TaISLab/pHRI-Hand-4F-Compliant/Pictures/IMG_0030.JPEG

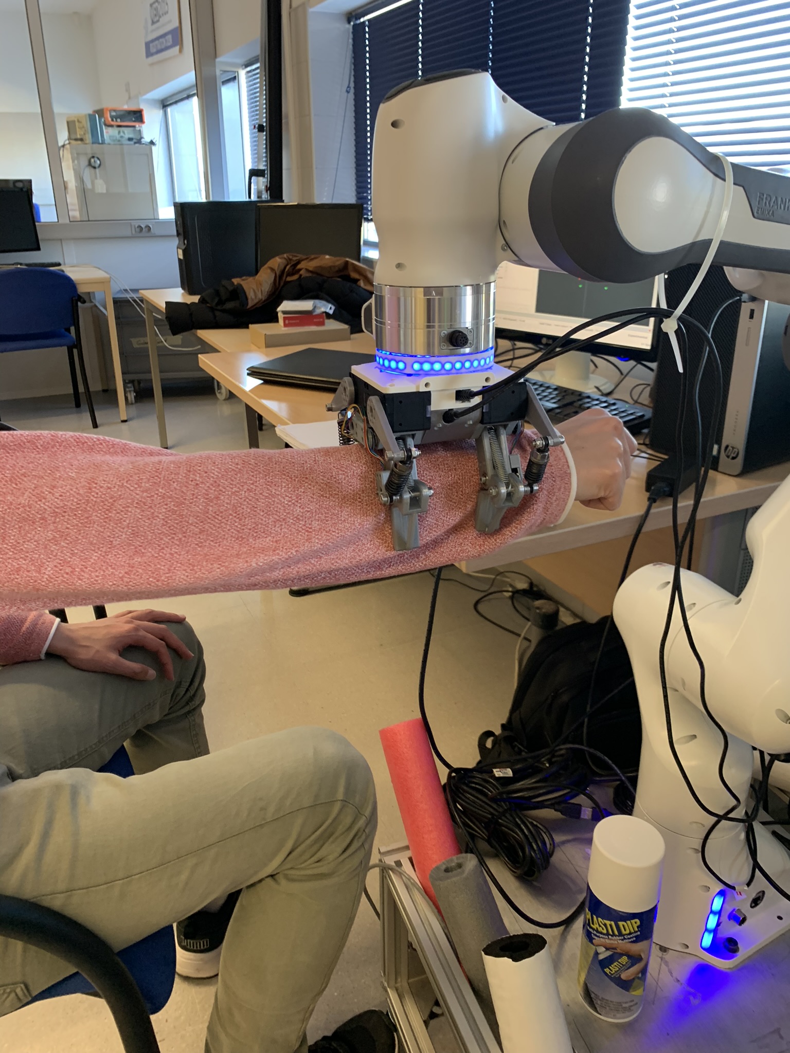
Pictures/IMG_0030.JPEG
