TaISLab/pHRI-Hand-4F-Compliant/CAD/base-servos.SLDPRT

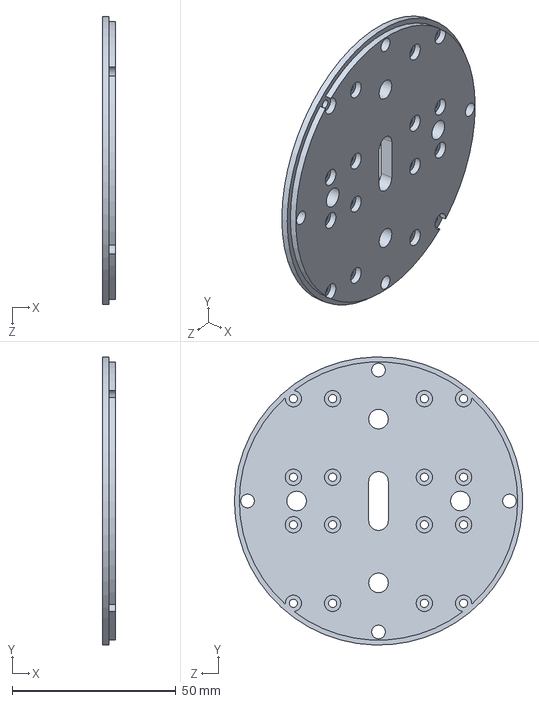
[picture p20: CAD file, 2024-05-29]
CAD/base-servos.SLDPRT
4.00 x 88.0 x 88.0 mm
