TaISLab/pHRI-Hand-4F-Compliant/CAD/potentiometers/potaxis.SLDPRT

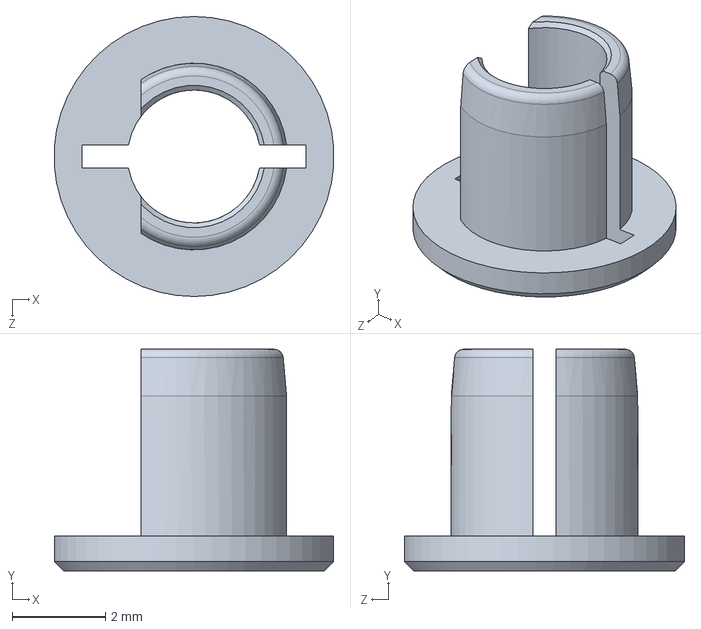
[picture p21: CAD file, 2024-05-29]
CAD/potentiometers/potaxis.SLDPRT
5.99 x 4.75 x 6.00 mm
