TaISLab/pHRI-Hand-4F-Compliant/CAD/Palo1.SLDPRT

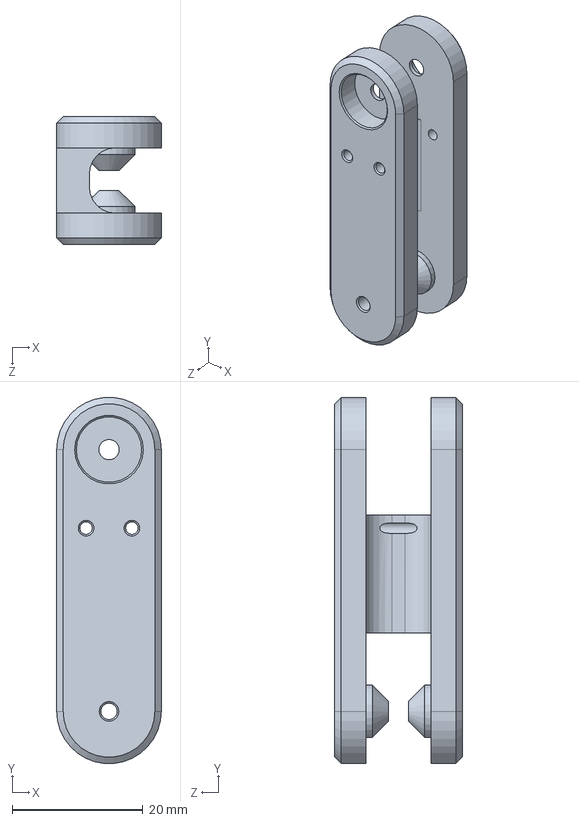
[picture p22: CAD file, 2024-05-29]
CAD/Palo1.SLDPRT
16.0 x 55.9 x 19.5 mm
