TaISLab/pHRI-Hand-4F-Compliant/CAD/biela servo.SLDPRT

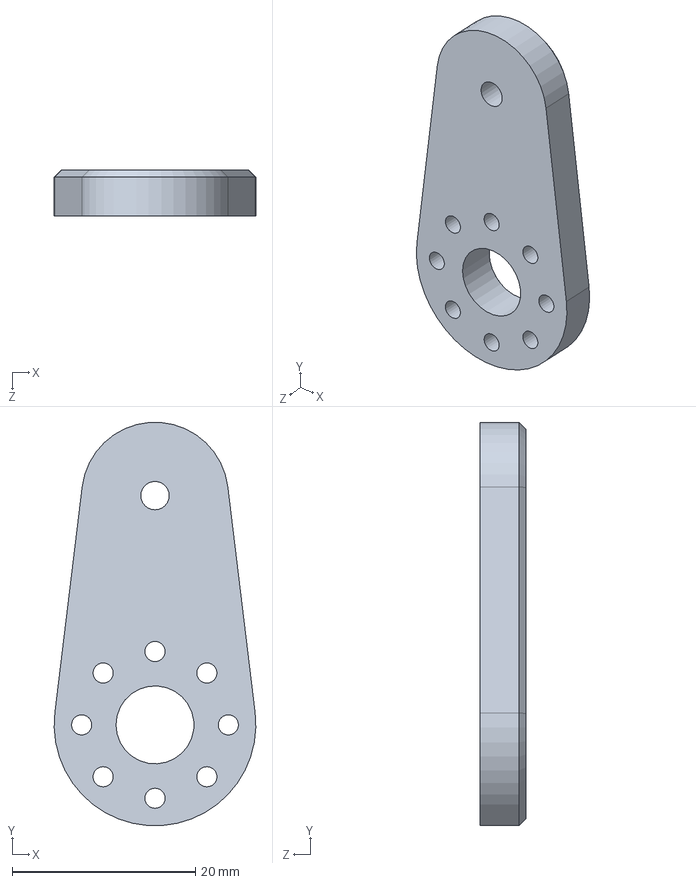
[picture p23: CAD file, 2024-05-29]
CAD/biela servo.SLDPRT
22.0 x 43.9 x 5.00 mm
