TaISLab/pHRI-Hand-4F-Compliant/CAD/Amortecedor (PRONTO).SLDPRT

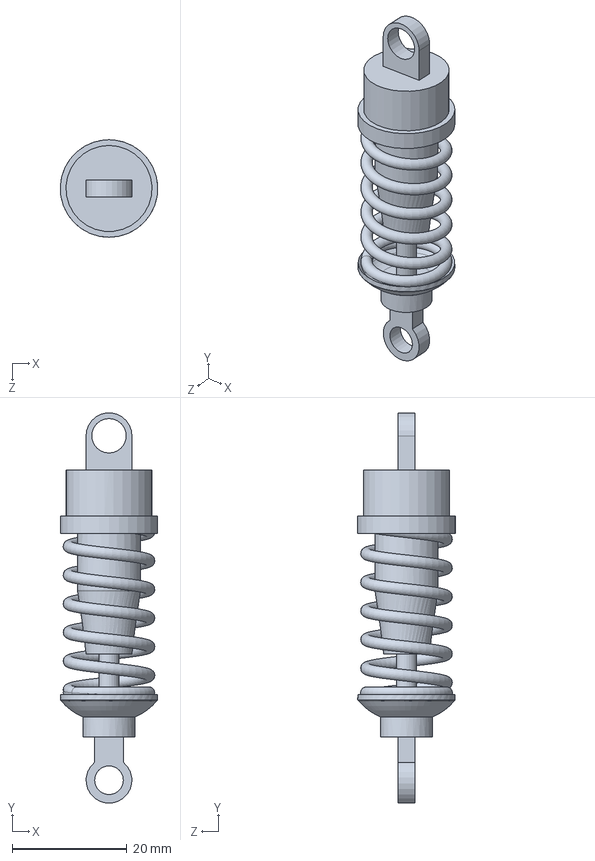
[picture p24: CAD file, 2024-05-29]
CAD/Amortecedor (PRONTO).SLDPRT
17.0 x 67.9 x 17.0 mm
