TaISLab/pHRI-Hand-4F-Compliant/CAD/biela servo 2-50.SLDPRT

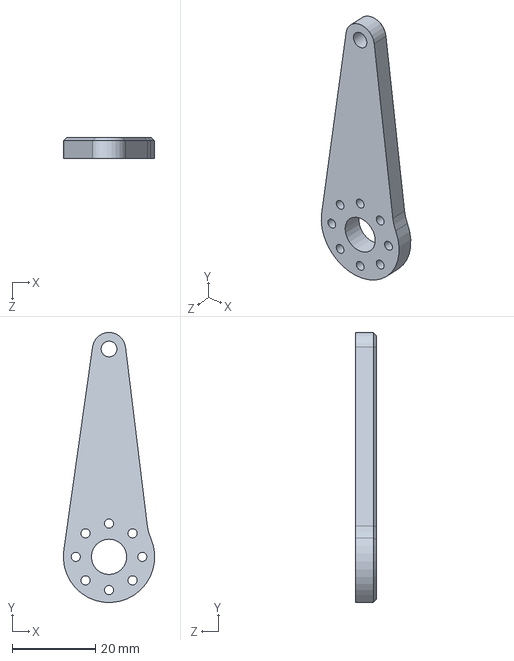
[picture p25: CAD file, 2024-05-29]
CAD/biela servo 2-50.SLDPRT
22.0 x 65.0 x 5.00 mm
