TaISLab/pHRI-Hand-4F-Compliant/CAD/base-robot-4.SLDPRT

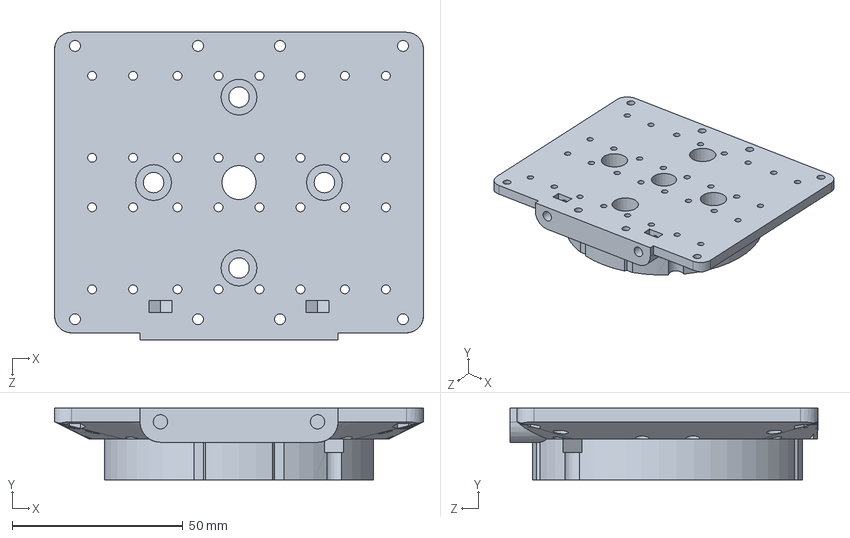
[picture p26: CAD file, 2024-05-29]
CAD/base-robot-4.SLDPRT
108.0 x 21.0 x 90.0 mm
