TaISLab/pHRI-Hand-4F-Compliant/CAD/biela servo 2-45.SLDPRT

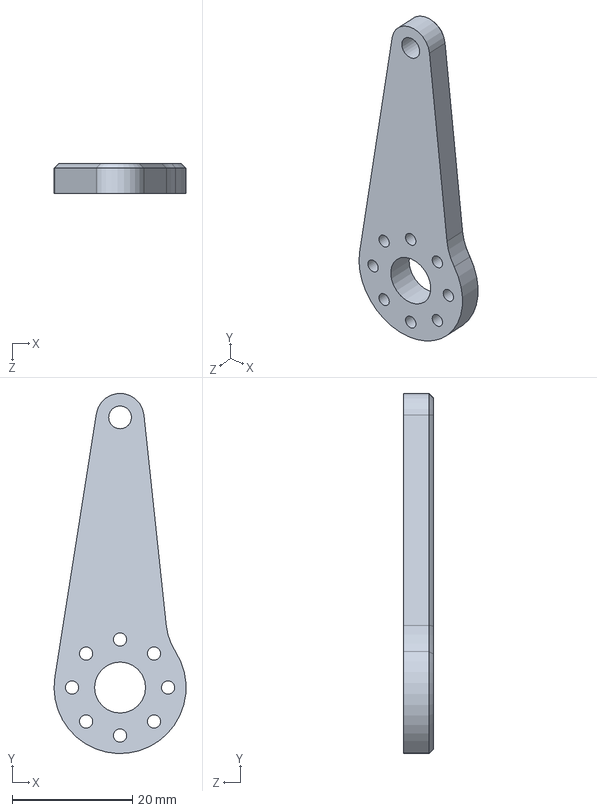
[picture p27: CAD file, 2024-05-29]
CAD/biela servo 2-45.SLDPRT
22.0 x 60.0 x 5.00 mm
