TaISLab/pHRI-Hand-4F-Compliant/CAD/Palo2.SLDPRT

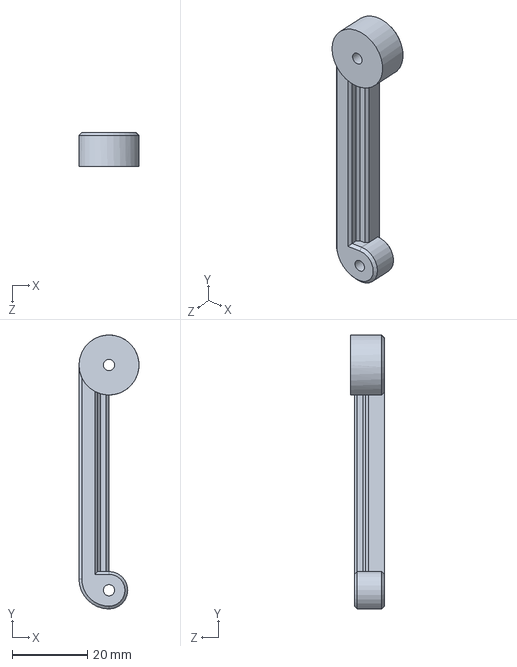
[picture p28: CAD file, 2024-05-29]
CAD/Palo2.SLDPRT
16.0 x 73.0 x 9.00 mm
