TaISLab/pHRI-Hand-4F-Compliant/CAD/pico20-ligero.SLDPRT

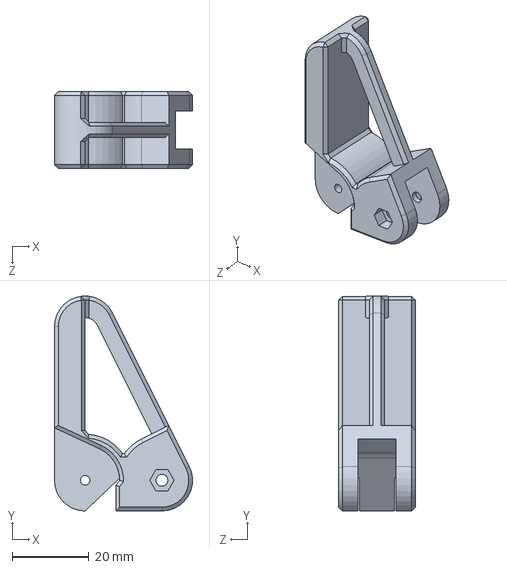
[picture p29: CAD file, 2024-05-29]
CAD/pico20-ligero.SLDPRT
36.0 x 56.0 x 20.0 mm
