TaISLab/pHRI-Hand-4F-Compliant/CAD/module.SLDPRT

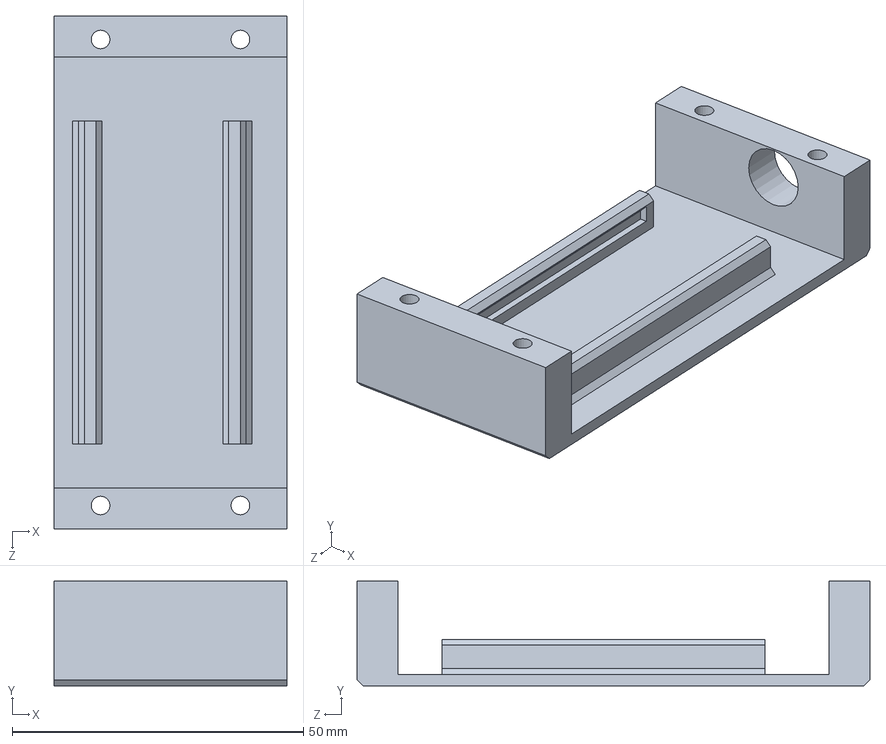
[picture p30: CAD file, 2024-05-29]
CAD/module.SLDPRT
40.0 x 18.0 x 88.0 mm
