TaISLab/pHRI-Hand-4F-Compliant/CAD/base-robot2.SLDPRT

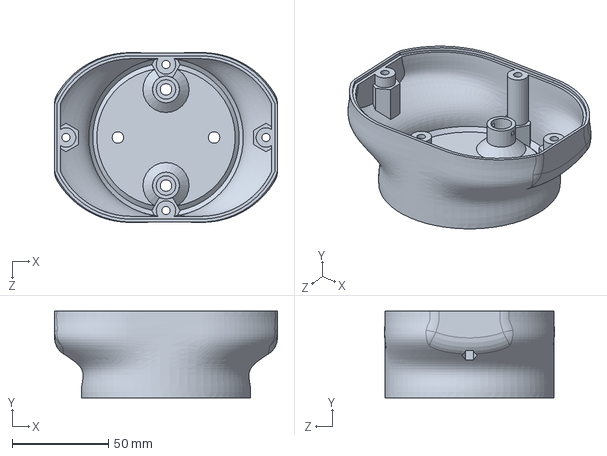
[picture p31: CAD file, 2024-05-29]
CAD/base-robot2.SLDPRT
116.0 x 45.0 x 88.3 mm
