TaISLab/pHRI-Hand-4F-Compliant/CAD/as5048a.SLDPRT

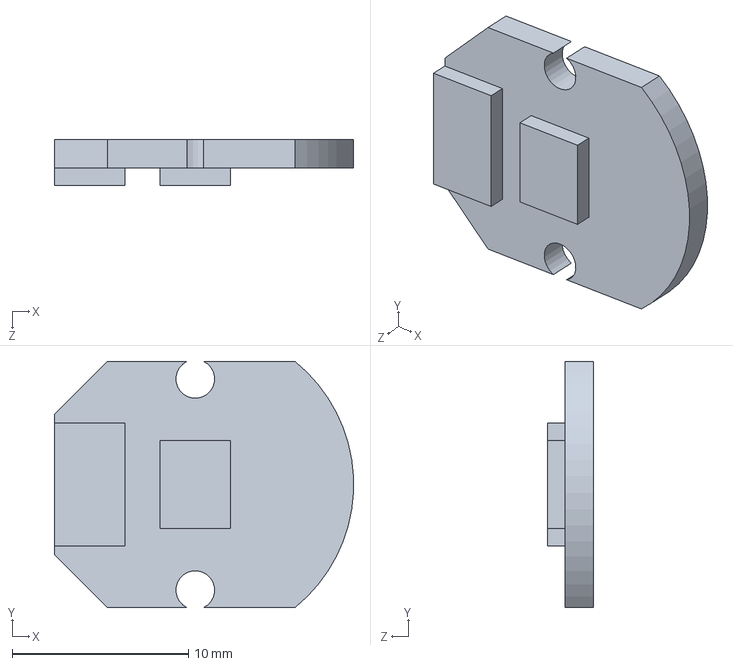
[picture p32: CAD file, 2024-05-29]
CAD/as5048a.SLDPRT
17.0 x 14.0 x 2.60 mm
