TaISLab/pHRI-Hand-4F-Compliant/CAD/biela servo 50.SLDPRT

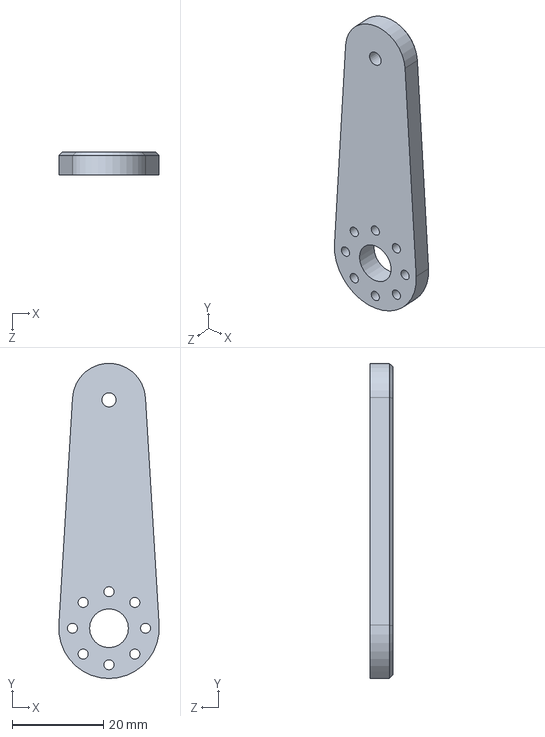
[picture p33: CAD file, 2024-05-29]
CAD/biela servo 50.SLDPRT
22.0 x 69.0 x 5.00 mm
