TaISLab/pHRI-Hand-4F-Compliant/CAD/baser-tobot-3.SLDPRT

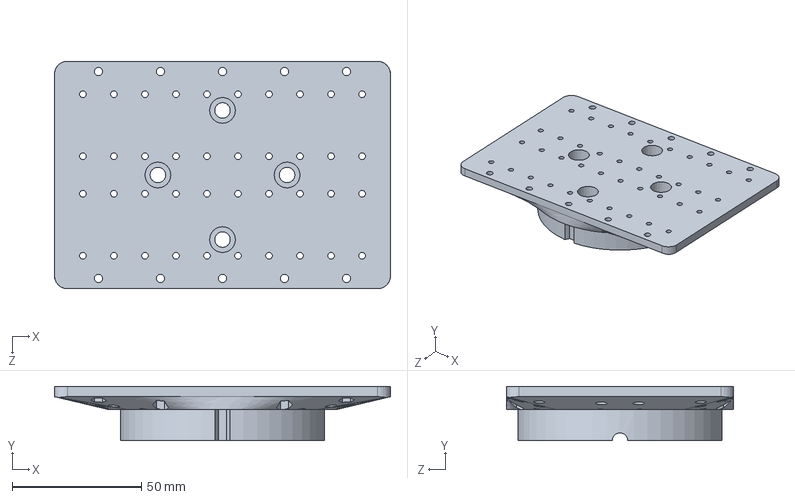
[picture p34: CAD file, 2024-05-29]
CAD/baser-tobot-3.SLDPRT
130.0 x 21.0 x 88.0 mm
