TaISLab/pHRI-Hand-4F-Compliant/CAD/biela servo 2.SLDPRT

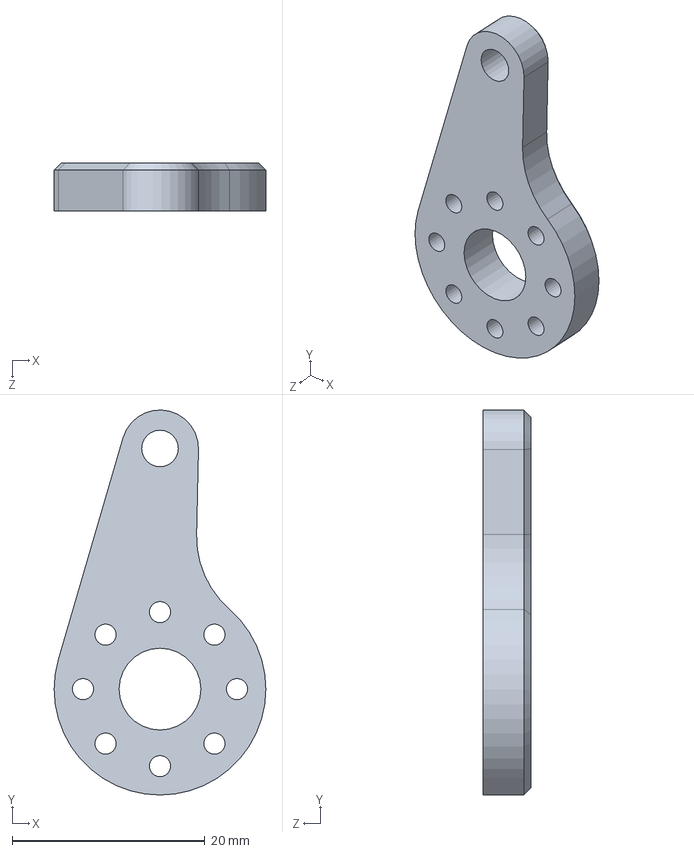
[picture p35: CAD file, 2024-05-29]
CAD/biela servo 2.SLDPRT
22.0 x 40.0 x 5.00 mm
