TaISLab/pHRI-Hand-4F-Compliant/CAD/biela servo 45.SLDPRT

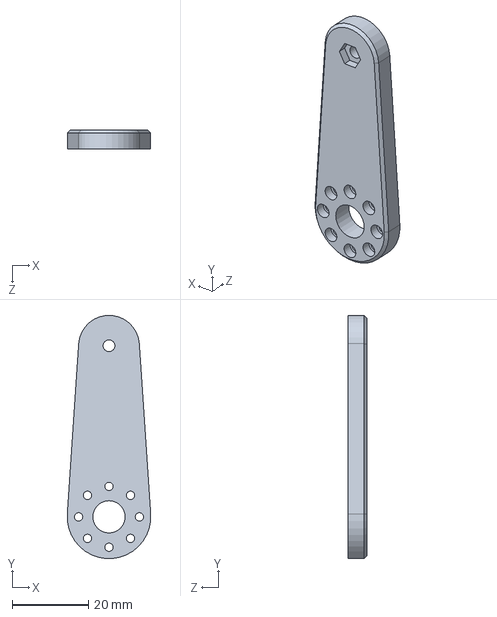
[picture p36: CAD file, 2024-05-29]
CAD/biela servo 45.SLDPRT
22.0 x 63.9 x 5.00 mm
