TaISLab/pHRI-Hand-4F-Compliant/CAD/forearm.SLDPRT

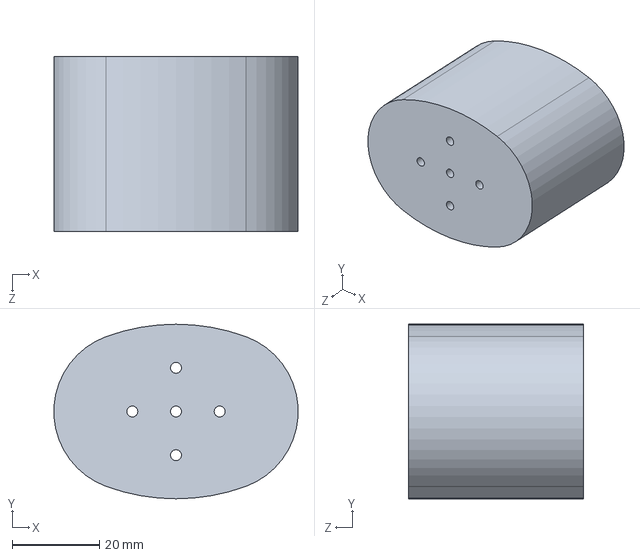
[picture p37: CAD file, 2024-05-29]
CAD/forearm.SLDPRT
55.9 x 40.0 x 40.0 mm
