TaISLab/pHRI-Hand-4F-Compliant/CAD/soporteencodersimple.SLDPRT

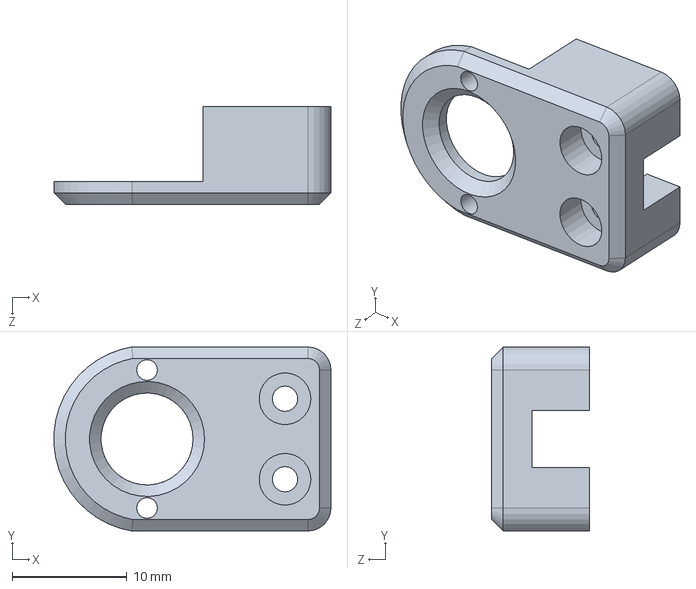
[picture p38: CAD file, 2024-05-29]
CAD/soporteencodersimple.SLDPRT
24.1 x 16.0 x 8.50 mm
