TaISLab/pHRI-Hand-4F-Compliant/CAD/soporteencoder.SLDPRT

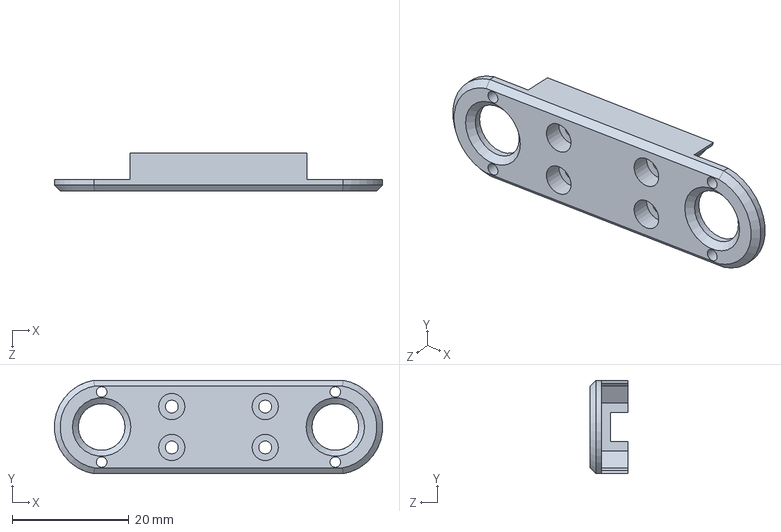
[picture p39: CAD file, 2024-05-29]
CAD/soporteencoder.SLDPRT
56.1 x 16.0 x 6.50 mm
