TaISLab/pHRI-Hand-4F-Compliant/CAD/module-chepa.SLDPRT

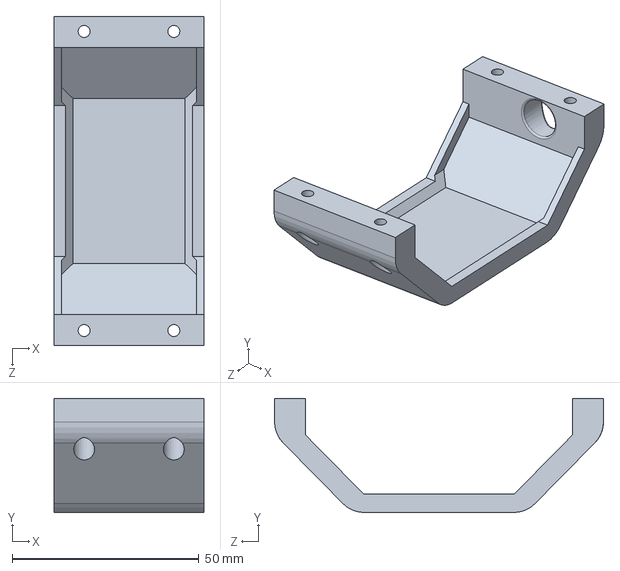
[picture p40: CAD file, 2024-05-29]
CAD/module-chepa.SLDPRT
40.0 x 30.5 x 88.0 mm
