TaISLab/pHRI-Hand-4F-Compliant/CAD/lgmount.SLDPRT

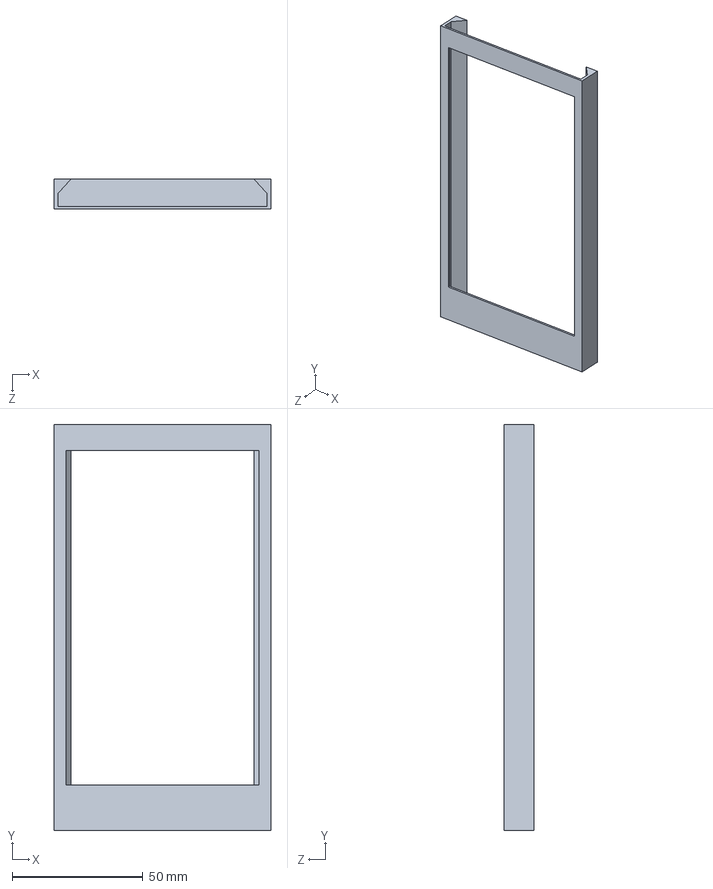
[picture p41: CAD file, 2024-05-29]
CAD/lgmount.SLDPRT
83.0 x 155.5 x 11.5 mm
