TaISLab/pHRI-Hand-4F-Compliant/CAD/base4.SLDPRT

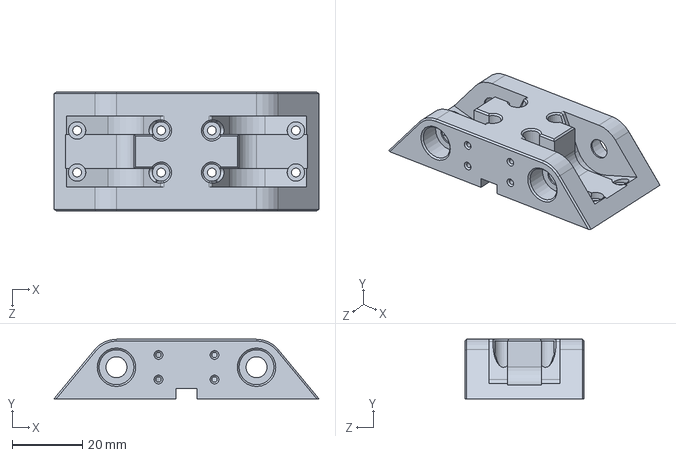
[picture p42: CAD file, 2024-05-29]
CAD/base4.SLDPRT
75.7 x 17.0 x 34.0 mm
