TaISLab/pHRI-Hand-4F-Compliant/CAD/biela servo 35.SLDPRT

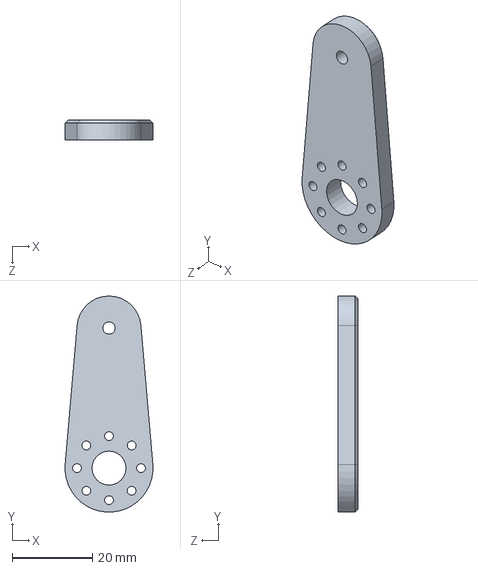
[picture p43: CAD file, 2024-05-29]
CAD/biela servo 35.SLDPRT
21.9 x 54.0 x 5.00 mm
