TaISLab/pHRI-Hand-4F-Compliant/CAD/pantalla led.SLDPRT

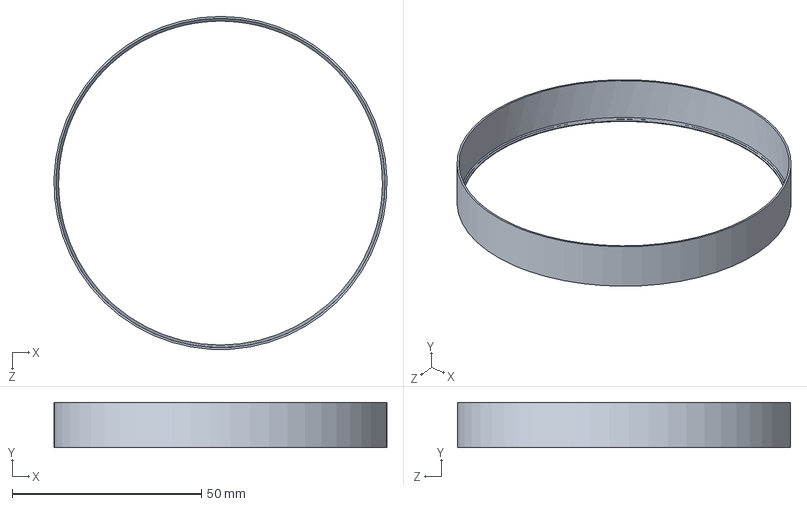
[picture p44: CAD file, 2024-05-29]
CAD/pantalla led.SLDPRT
88.0 x 12.0 x 88.0 mm
