TaISLab/pHRI-Hand-4F-Compliant/CAD/base-robot.SLDPRT

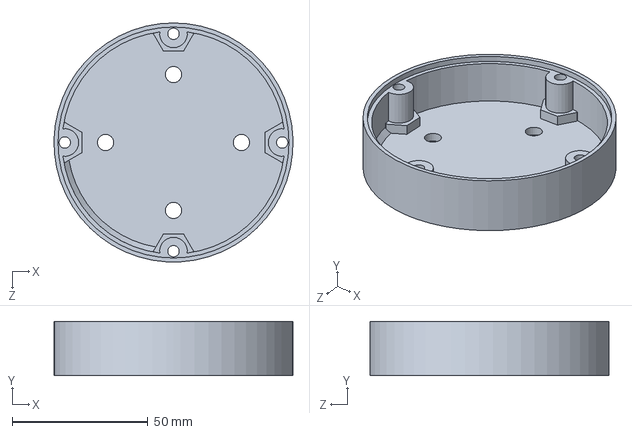
[picture p45: CAD file, 2024-05-29]
CAD/base-robot.SLDPRT
88.0 x 20.0 x 88.0 mm
