TaISLab/pHRI-Hand-4F-Compliant/CAD/acopla-top.SLDPRT

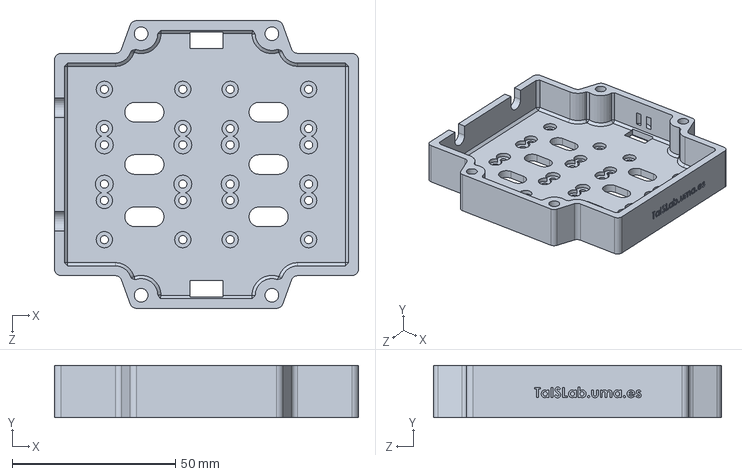
[picture p46: CAD file, 2024-05-29]
CAD/acopla-top.SLDPRT
93.0 x 16.0 x 88.0 mm
