TaISLab/pHRI-Hand-4F-Compliant/CAD/potBASE2.SLDPRT

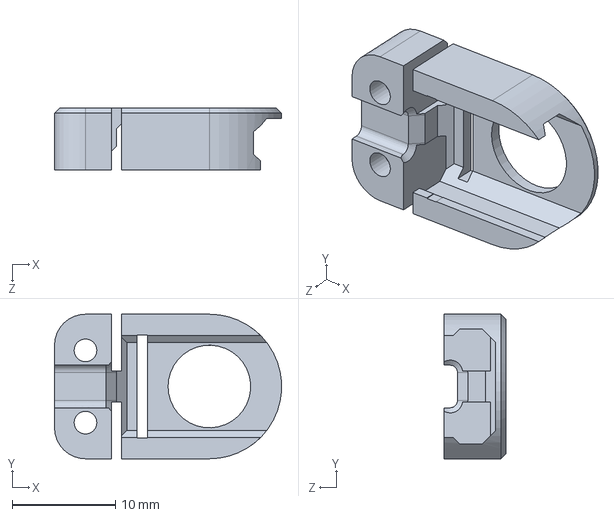
[picture p47: CAD file, 2024-05-29]
CAD/potBASE2.SLDPRT
22.0 x 14.0 x 6.00 mm
