TaISLab/pHRI-Hand-4F-Compliant/CAD/Axis_4mm.SLDPRT

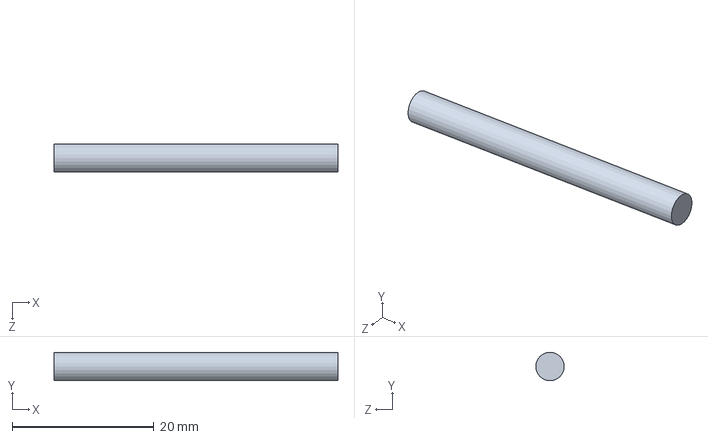
[picture p48: CAD file, 2024-05-29]
CAD/Axis_4mm.SLDPRT
40.0 x 4.00 x 4.00 mm
