TaISLab/pHRI-Hand-4F-Compliant/CAD/Palo2 85mm.SLDPRT

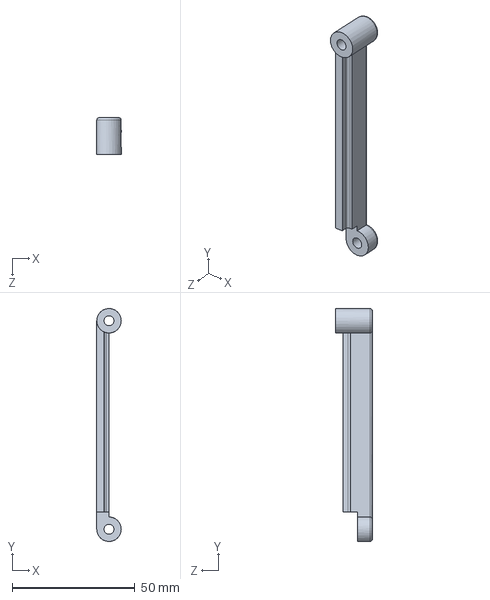
[picture p49: CAD file, 2024-05-29]
CAD/Palo2 85mm.SLDPRT
10.0 x 95.0 x 15.0 mm
