TaISLab/pHRI-Hand-4F-Compliant/CAD/Biela Servo 40 mm.SLDPRT

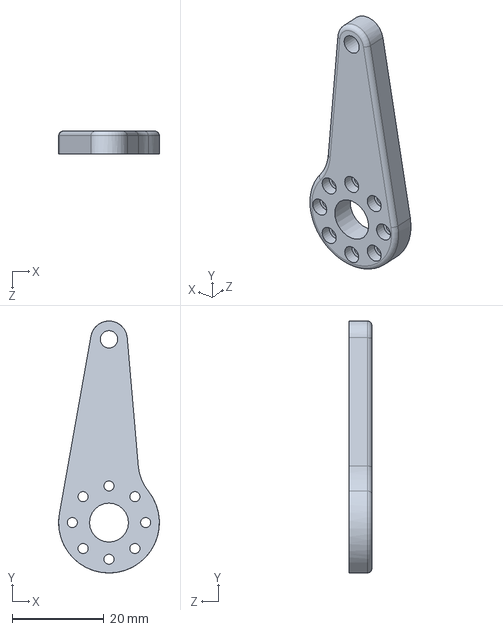
[picture p50: CAD file, 2024-05-29]
CAD/Biela Servo 40 mm.SLDPRT
22.0 x 55.0 x 5.00 mm
