TaISLab/pHRI-Hand-4F-Compliant/CAD/base4_mod.SLDPRT

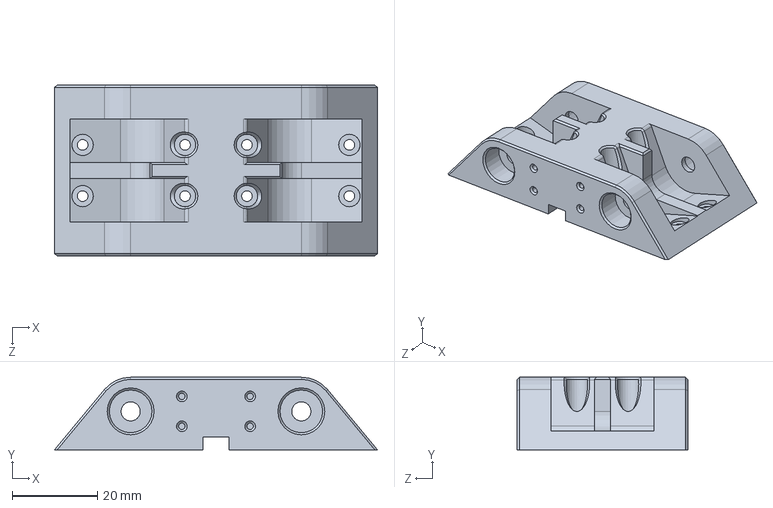
[picture p51: CAD file, 2024-05-29]
CAD/base4_mod.SLDPRT
75.7 x 17.0 x 40.0 mm
