TaISLab/pHRI-Hand-4F-Compliant/CAD/phalanx2_v7.SLDPRT

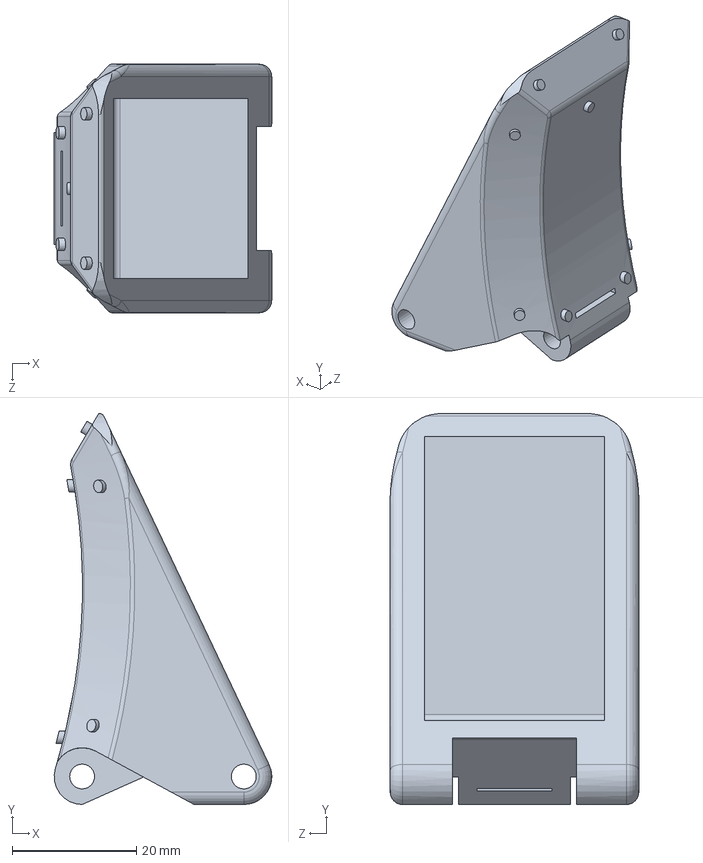
[picture p52: CAD file, 2024-05-29]
CAD/phalanx2_v7.SLDPRT
35.0 x 62.9 x 40.0 mm
