TaISLab/pHRI-Hand-4F-Compliant/CAD/phalanx1_v8.SLDPRT

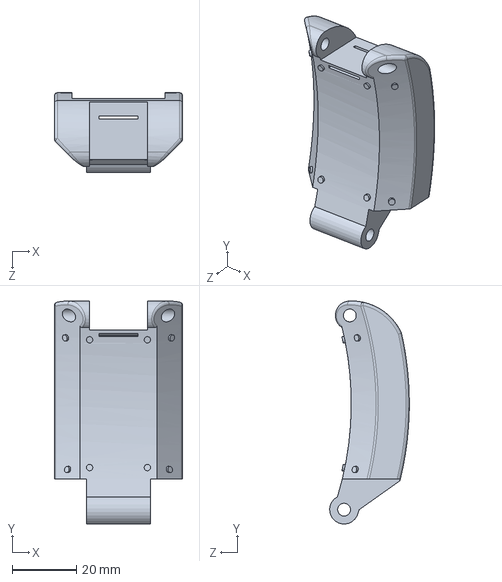
[picture p53: CAD file, 2024-05-29]
CAD/phalanx1_v8.SLDPRT
40.0 x 69.5 x 24.8 mm
