TaISLab/pHRI-Hand-4F-Compliant/CAD/module-chepa_mod.SLDPRT

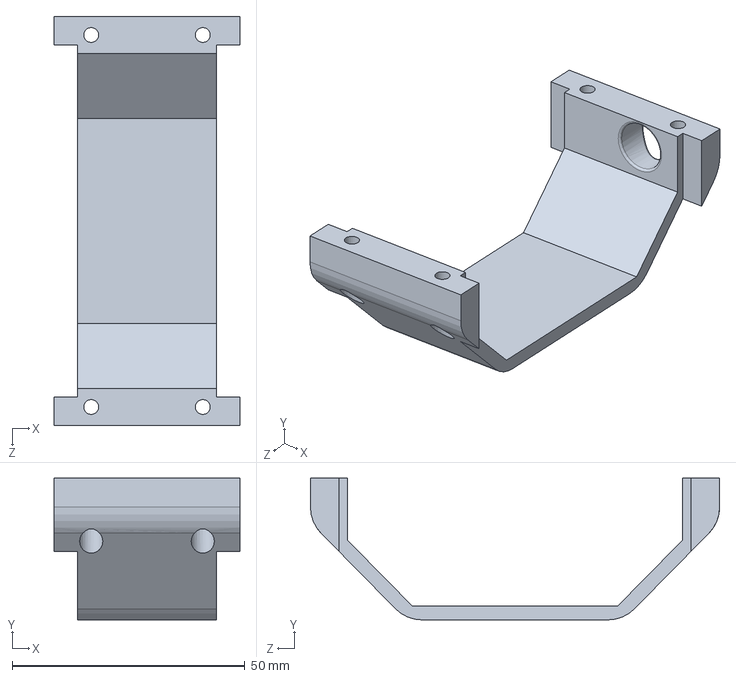
[picture p54: CAD file, 2024-05-29]
CAD/module-chepa_mod.SLDPRT
40.0 x 30.5 x 88.0 mm
