TaISLab/pHRI-Hand-4F-Compliant/CAD/Modelo_brazo_notwist.SLDPRT

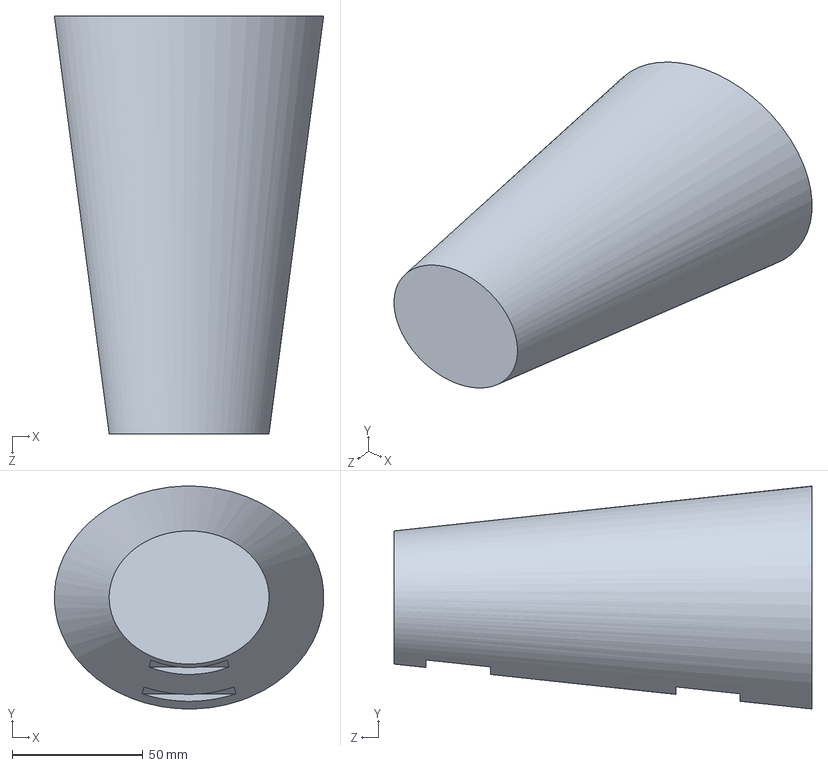
[picture p55: CAD file, 2024-05-29]
CAD/Modelo_brazo_notwist.SLDPRT
103.1 x 85.3 x 160.0 mm
